superbad64/OpenFighter/Personal Builds/Final Boss Neo/STL/Long sides/side_none.stl

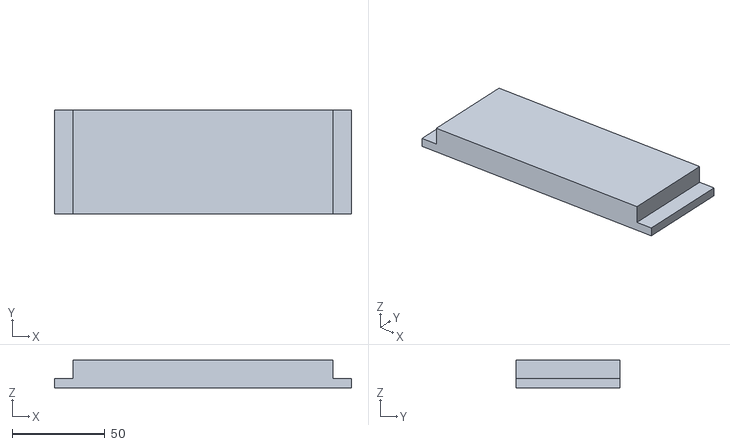
[picture p22: CAD file, 2025-08-16]
Personal Builds/Final Boss Neo/STL/Long sides/side_none.stl
160.0 x 56.0 x 15.0
