superbad64/OpenFighter/Personal Builds/Miniboss Neo/Cut files/miniboss_neo.dxf

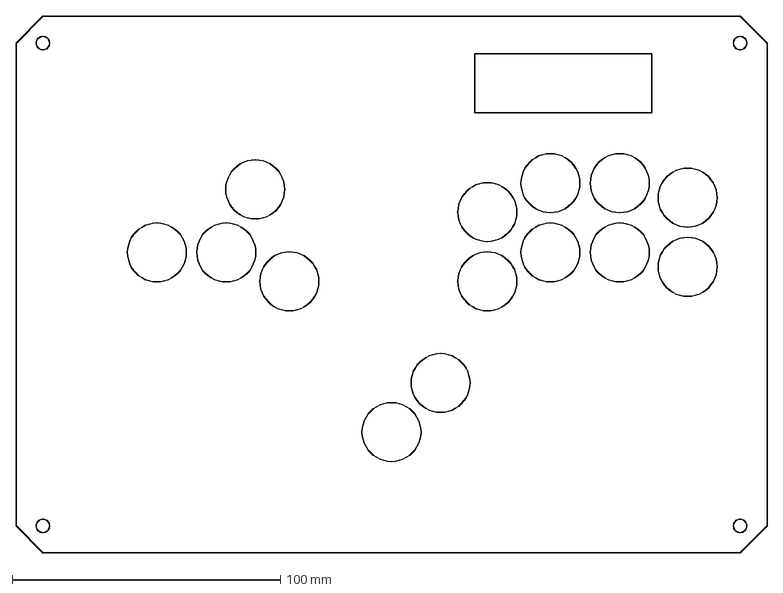
[picture p24: CAD file, 2025-08-24]
Personal Builds/Miniboss Neo/Cut files/miniboss_neo.dxf
280.0 x 200.0 mm
