superbad64/OpenFighter/Personal Builds/Raijin/Production Files/corner.stl

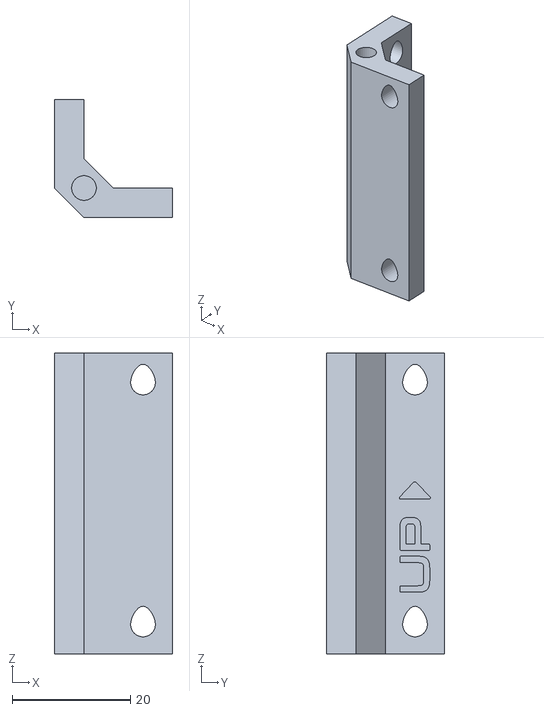
[picture p25: CAD file, 2025-08-24]
Personal Builds/Raijin/Production Files/corner.stl
20.0 x 20.0 x 51.0
