superbad64/OpenFighter/Personal Builds/Raijin/Production Files/Cuts/raijin.spacer.dxf

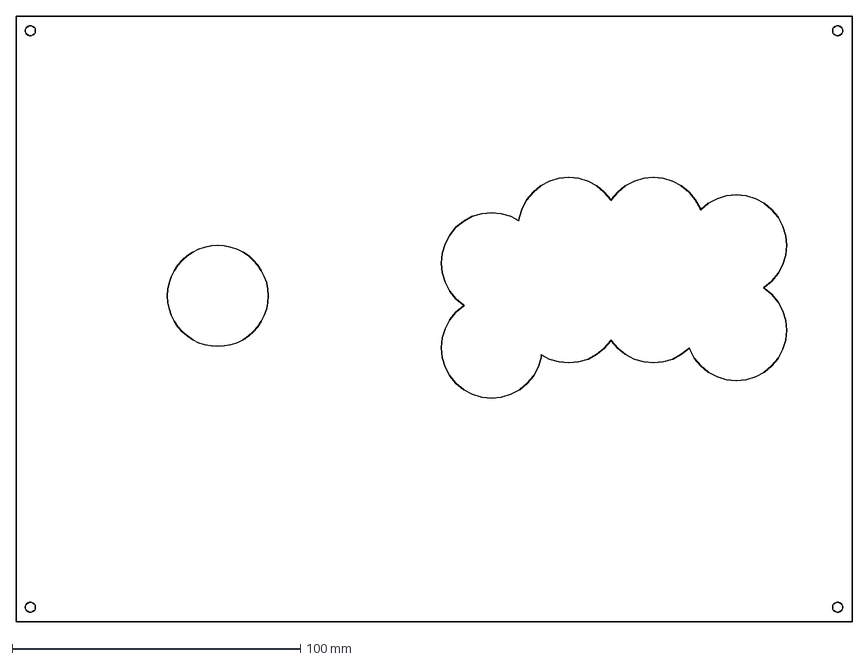
[picture p26: CAD file, 2026-04-07]
Personal Builds/Raijin/Production Files/Cuts/raijin.spacer.dxf
290.0 x 210.0 mm
