superbad64/OpenFighter/Tteokbokki/STL/Bottom Panels/Magnetic/magnetic_bottom_right.stl

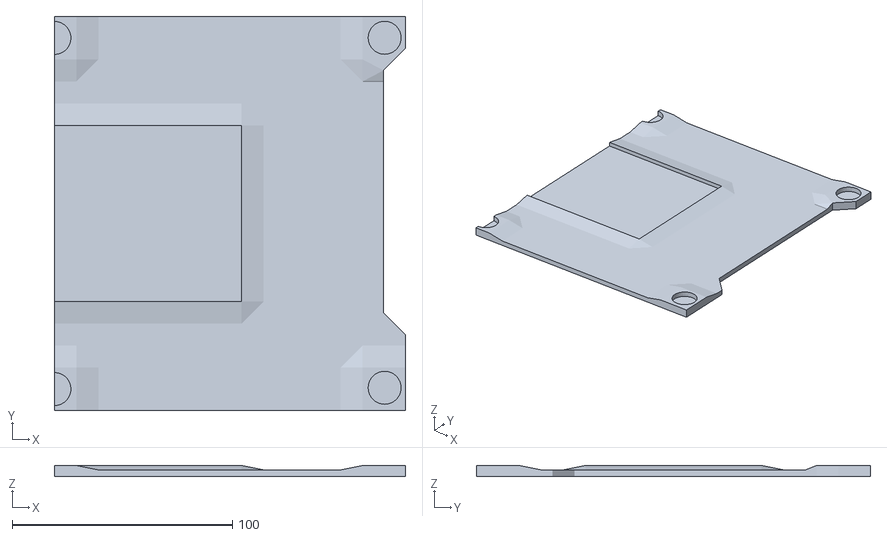
[picture p27: CAD file, 2025-12-30]
Tteokbokki/STL/Bottom Panels/Magnetic/magnetic_bottom_right.stl
159.5 x 179.0 x 5.00
