superbad64/OpenFighter/Tteokbokki/STL/Top Panels/Hitbox/hb_right.stl

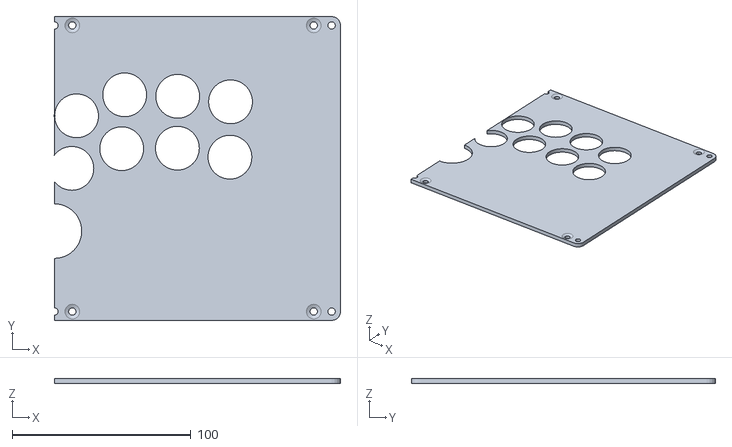
[picture p28: CAD file, 2025-12-30]
Tteokbokki/STL/Top Panels/Hitbox/hb_right.stl
160.0 x 170.0 x 3.00
