superbad64/OpenFighter/Tteokbokki/STL/Top Panels/Sega 2P/30mm/s2p_30mm_left.stl

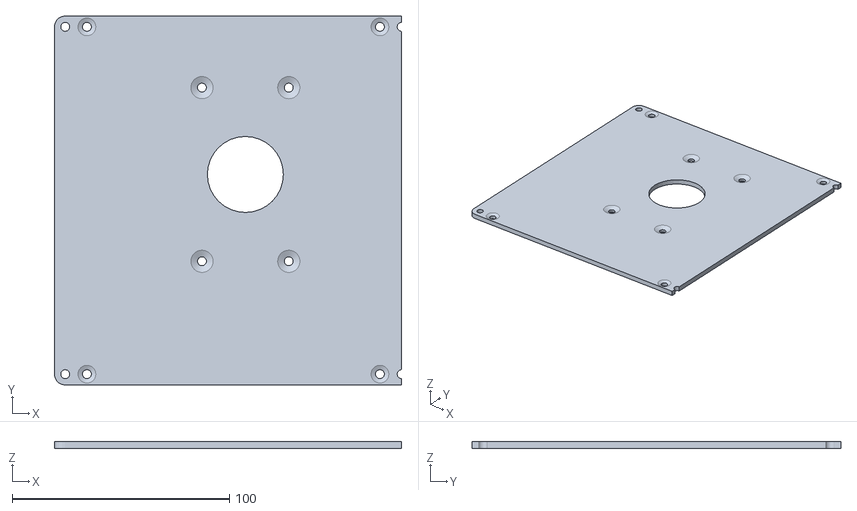
[picture p29: CAD file, 2025-12-30]
Tteokbokki/STL/Top Panels/Sega 2P/30mm/s2p_30mm_left.stl
160.0 x 170.0 x 3.00
