superbad64/OpenFighter/Tteokbokki/STL/Top Panels/WASD/wasd_right.stl

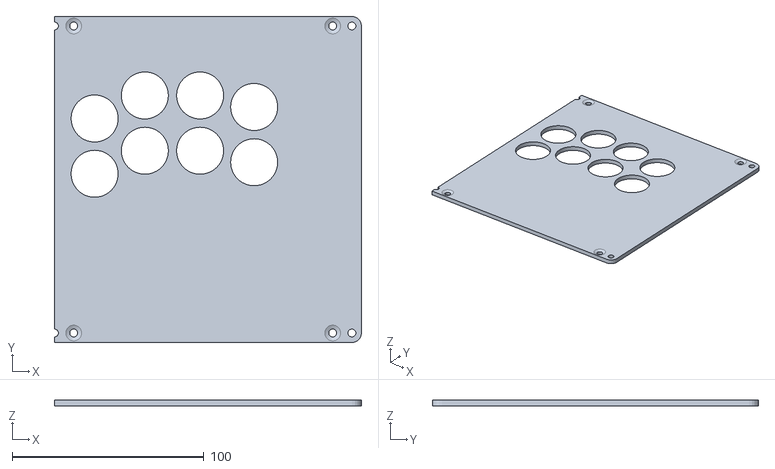
[picture p30: CAD file, 2025-12-30]
Tteokbokki/STL/Top Panels/WASD/wasd_right.stl
160.0 x 170.0 x 3.00
