superbad64/OpenFighter/Unhinged/Cut files/WASD.dxf

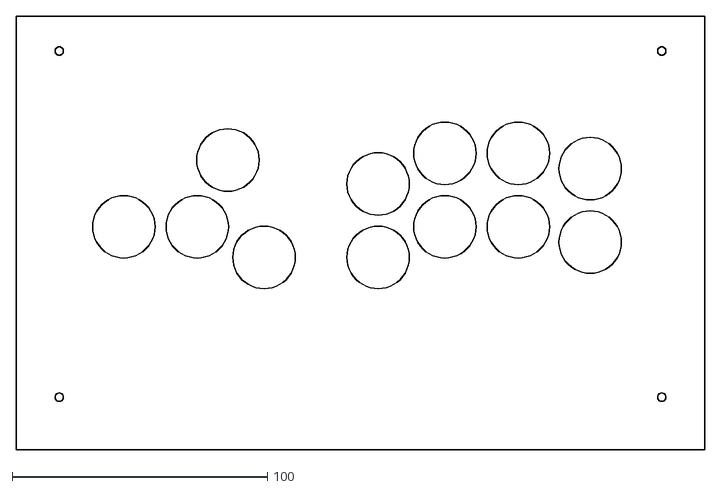
[picture p31: CAD file, 2025-08-24]
Unhinged/Cut files/WASD.dxf
270.0 x 169.9
