superbad64/OpenFighter/Unhinged/STL/Hinges/long arm.stl

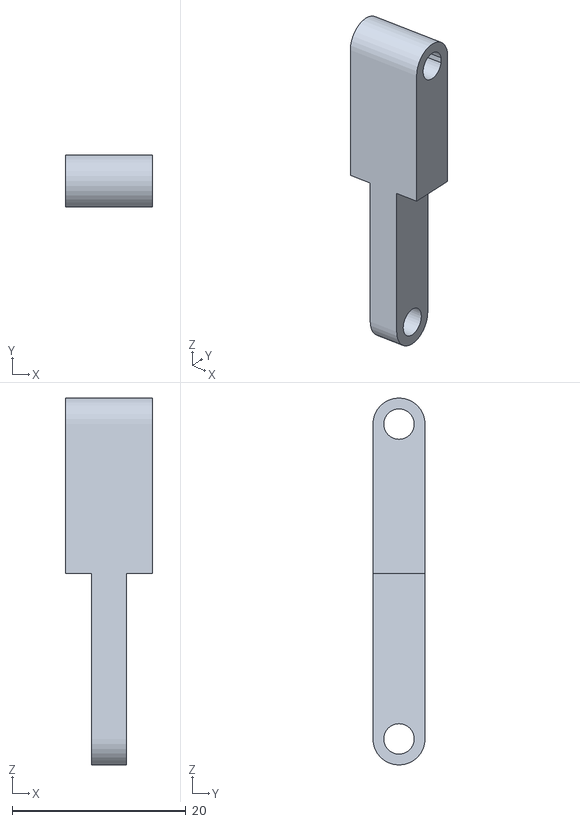
[picture p32: CAD file, 2025-02-27]
Unhinged/STL/Hinges/long arm.stl
10.0 x 6.00 x 42.2
