superbad64/OpenFighter/Unhinged/STL/left.stl

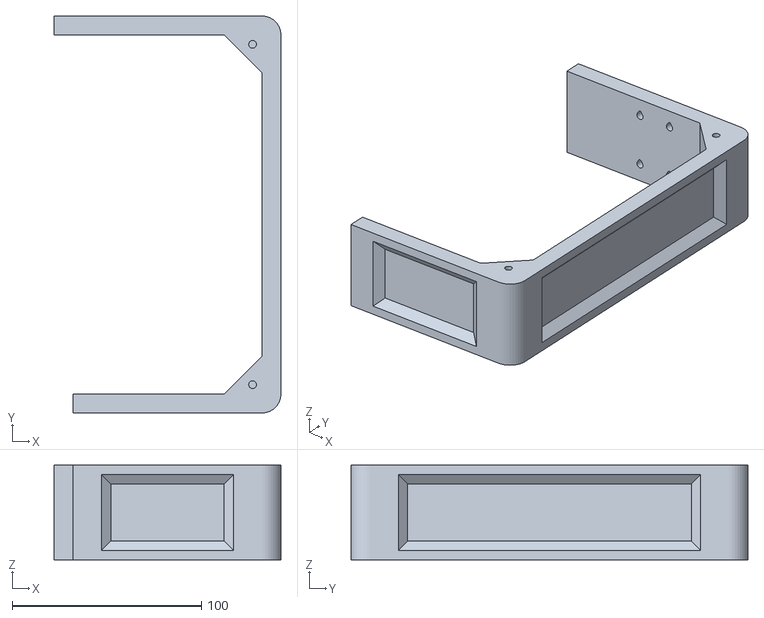
[picture p33: CAD file, 2025-02-27]
Unhinged/STL/left.stl
120.0 x 210.0 x 50.0
