superbad64/OpenFighter/Unhinged/STL/Top/pin.stl

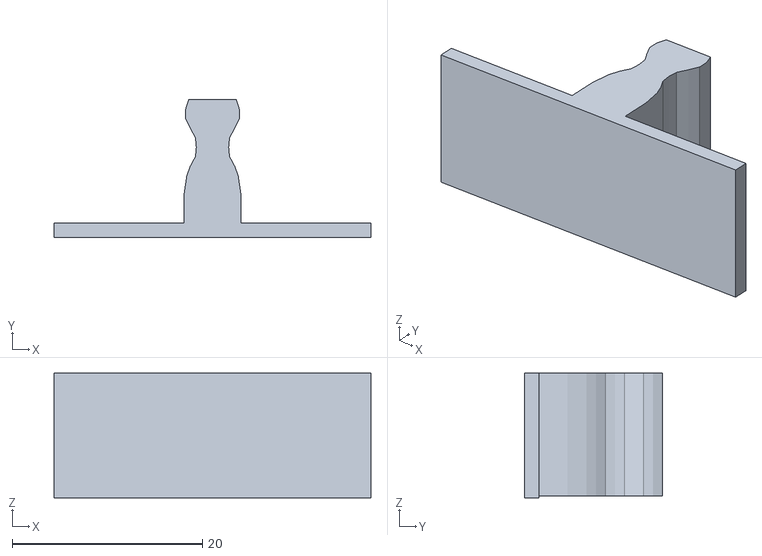
[picture p34: CAD file, 2025-02-27]
Unhinged/STL/Top/pin.stl
33.4 x 14.5 x 13.1
