superbad64/OpenFighter/Wanderer/Production Files/STL/right.stl

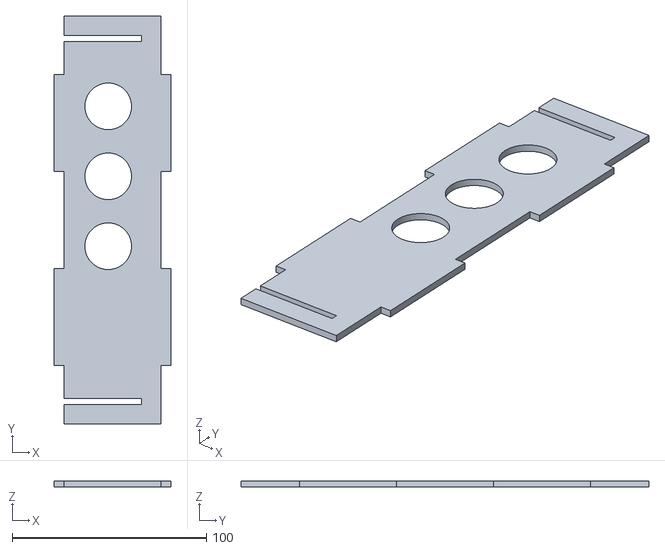
[picture p35: CAD file, 2025-12-16]
Wanderer/Production Files/STL/right.stl
60.0 x 210.0 x 3.00
