superbad64/OpenFighter/Ogre/Production Files/Laser Cut Templates/wing external.dxf

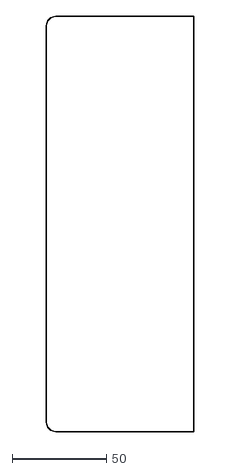
[picture p37: CAD file, 2025-08-24]
Ogre/Production Files/Laser Cut Templates/wing external.dxf
78.0 x 220.0
