superbad64/OpenFighter/Ogre/Production Files/STL/Common/bottom.stl

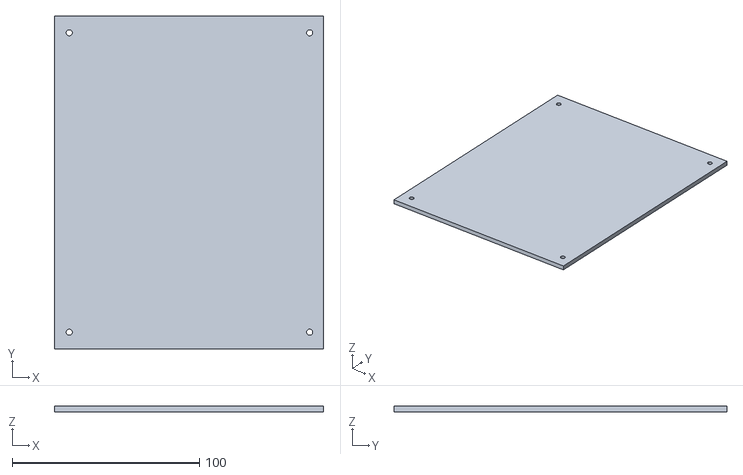
[picture p38: CAD file, 2025-02-27]
Ogre/Production Files/STL/Common/bottom.stl
144.0 x 178.0 x 3.00
