superbad64/OpenFighter/Ork/Production Files/shortside.stl

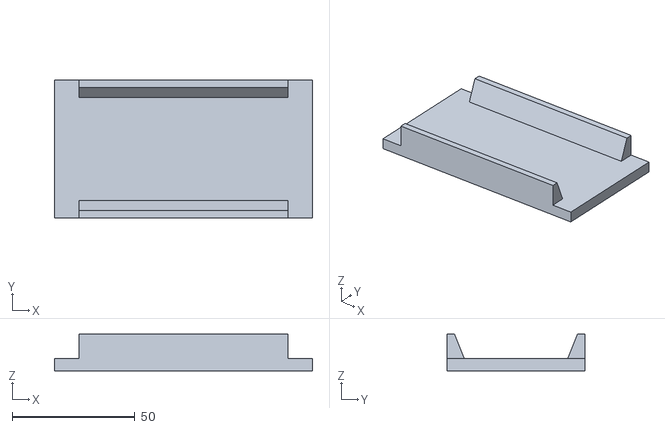
[picture p40: CAD file, 2025-08-16]
Ork/Production Files/shortside.stl
105.0 x 56.0 x 15.0
