superbad64/OpenFighter/Ork/Production Files/WASD/wasd_topright.stl

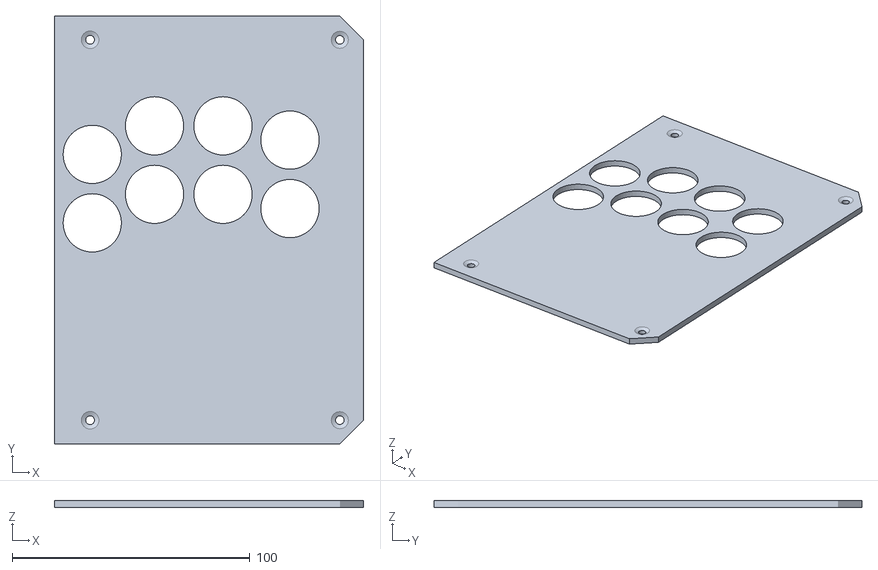
[picture p41: CAD file, 2025-08-16]
Ork/Production Files/WASD/wasd_topright.stl
130.0 x 180.0 x 3.00
