superbad64/OpenFighter/Personal Builds/Final Boss Neo/Laser Cuts/fbneo.topright.dxf

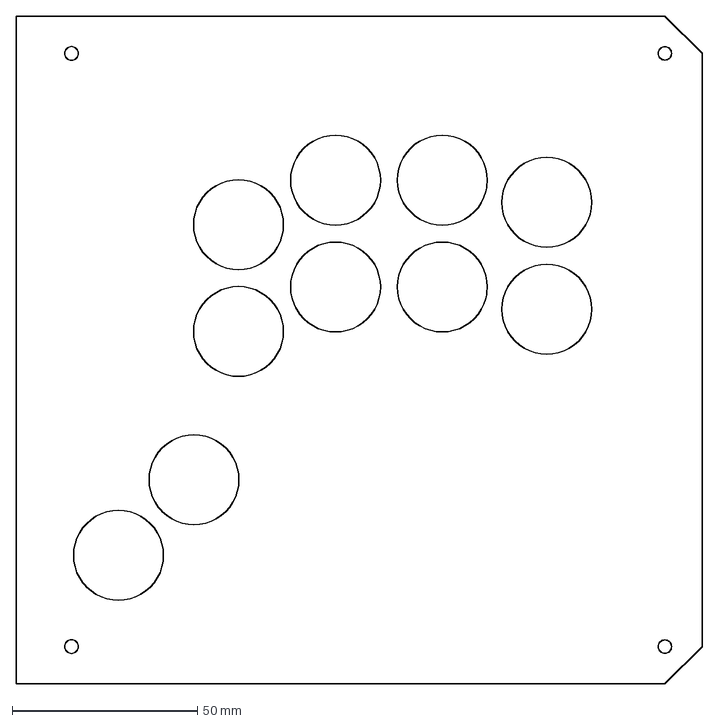
[picture p42: CAD file, 2025-08-24]
Personal Builds/Final Boss Neo/Laser Cuts/fbneo.topright.dxf
185.0 x 180.0 mm
