superbad64/OpenFighter/Personal Builds/Final Boss Neo/STL/Long sides/side_vent.stl

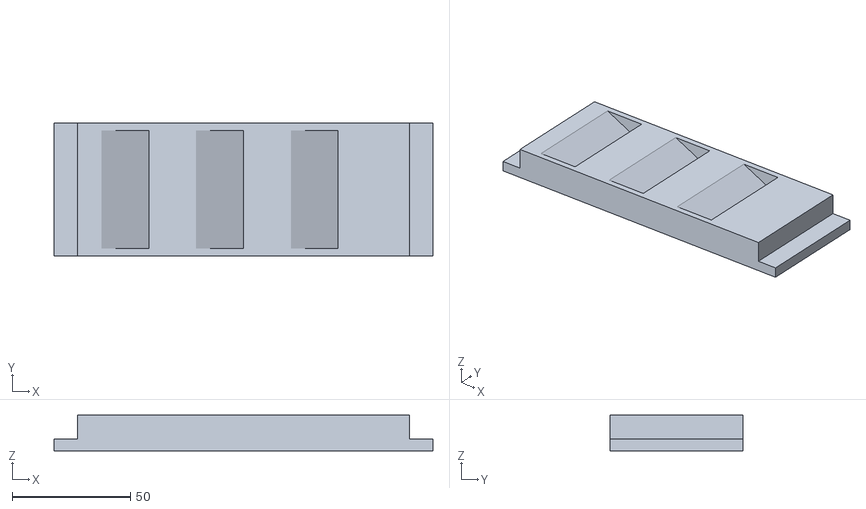
[picture p43: CAD file, 2025-08-16]
Personal Builds/Final Boss Neo/STL/Long sides/side_vent.stl
160.0 x 56.0 x 15.0
