superbad64/OpenFighter/Personal Builds/Final Boss Neo/STL/Surround Plates/surround_nunchuk_backplate.stl

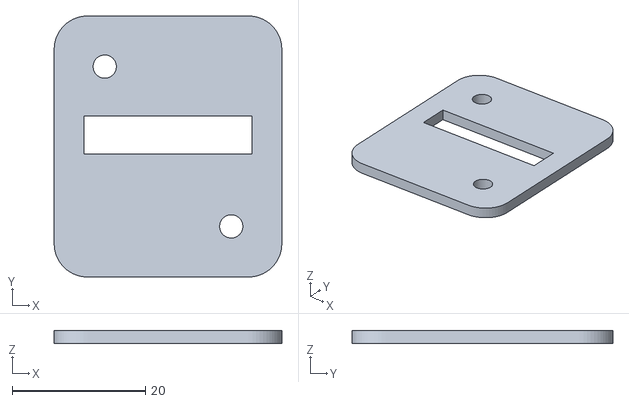
[picture p44: CAD file, 2025-08-16]
Personal Builds/Final Boss Neo/STL/Surround Plates/surround_nunchuk_backplate.stl
34.2 x 39.2 x 2.00
