superbad64/OpenFighter/Personal Builds/Final Boss Neo/STL/top_right.stl

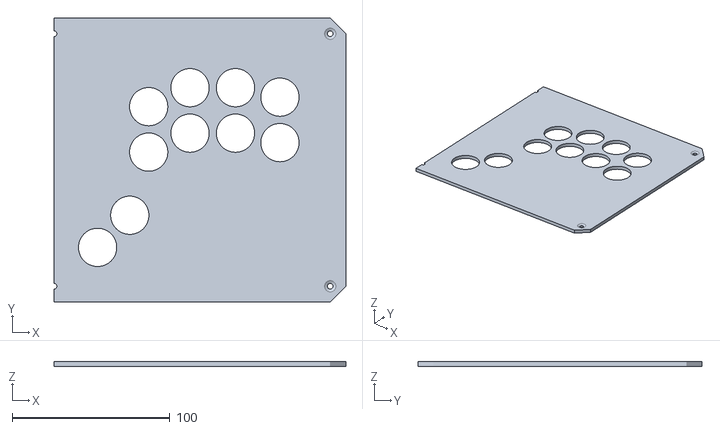
[picture p45: CAD file, 2025-08-16]
Personal Builds/Final Boss Neo/STL/top_right.stl
185.0 x 180.0 x 3.00
