superbad64/OpenFighter/Personal Builds/Raijin/Production Files/bracket.stl

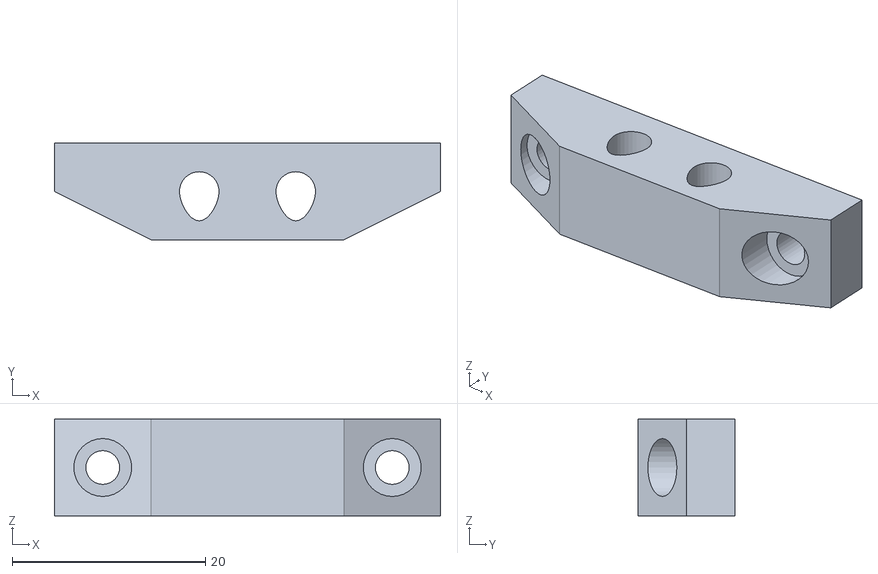
[picture p46: CAD file, 2025-08-24]
Personal Builds/Raijin/Production Files/bracket.stl
40.0 x 10.0 x 10.0
