superbad64/OpenFighter/Personal Builds/Raijin/Production Files/Cuts/raijin.dxf

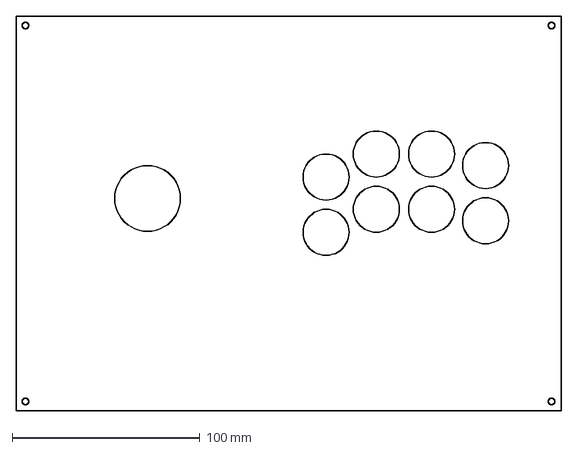
[picture p47: CAD file, 2025-08-24]
Personal Builds/Raijin/Production Files/Cuts/raijin.dxf
290.0 x 210.0 mm
