superbad64/OpenFighter/Tteokbokki/STL/Top Panels/Hitbox/hb_left.stl

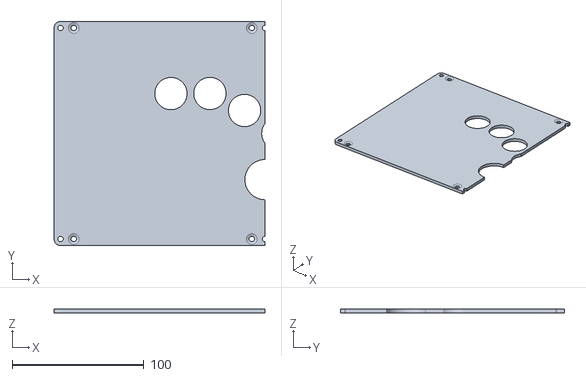
[picture p48: CAD file, 2025-12-30]
Tteokbokki/STL/Top Panels/Hitbox/hb_left.stl
160.0 x 170.0 x 3.00
