superbad64/OpenFighter/Unhinged/Cut files/Sega 2P.dxf

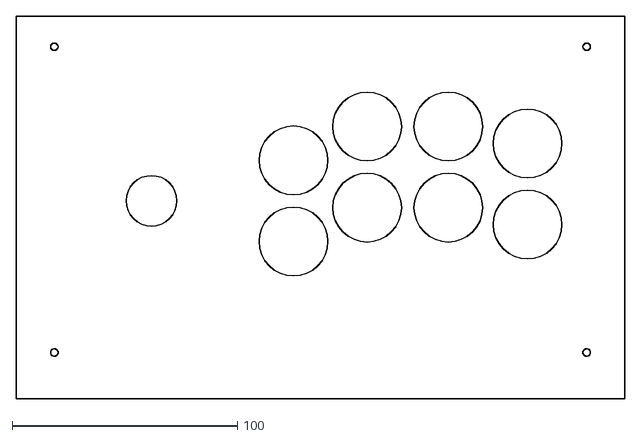
[picture p50: CAD file, 2025-08-24]
Unhinged/Cut files/Sega 2P.dxf
270.0 x 169.9
