superbad64/OpenFighter/Unhinged/STL/bottomright.stl

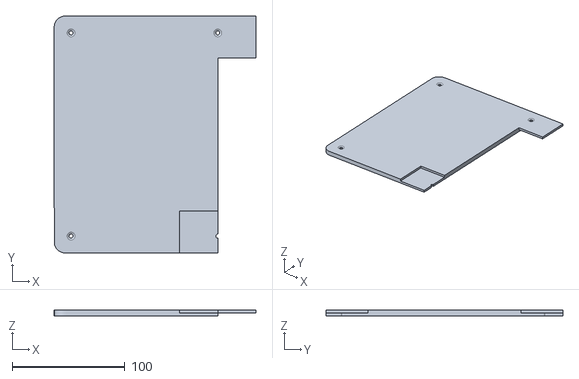
[picture p51: CAD file, 2025-02-27]
Unhinged/STL/bottomright.stl
178.8 x 210.0 x 5.00
