superbad64/OpenFighter/Unhinged/STL/Hinges/hinge base.stl

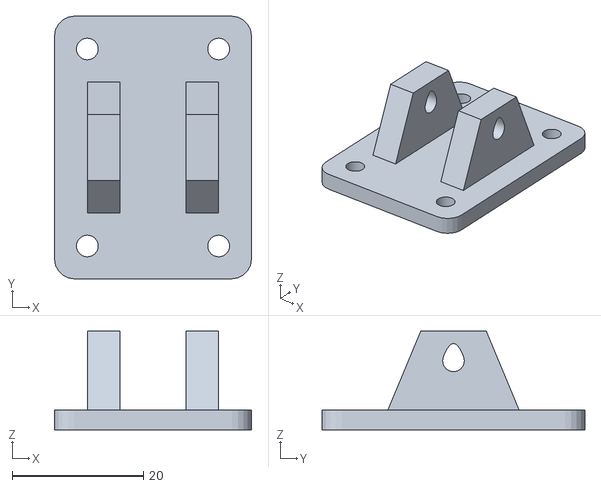
[picture p52: CAD file, 2025-02-27]
Unhinged/STL/Hinges/hinge base.stl
30.0 x 40.0 x 15.0
