superbad64/OpenFighter/Unhinged/STL/Top/bezel_right.stl

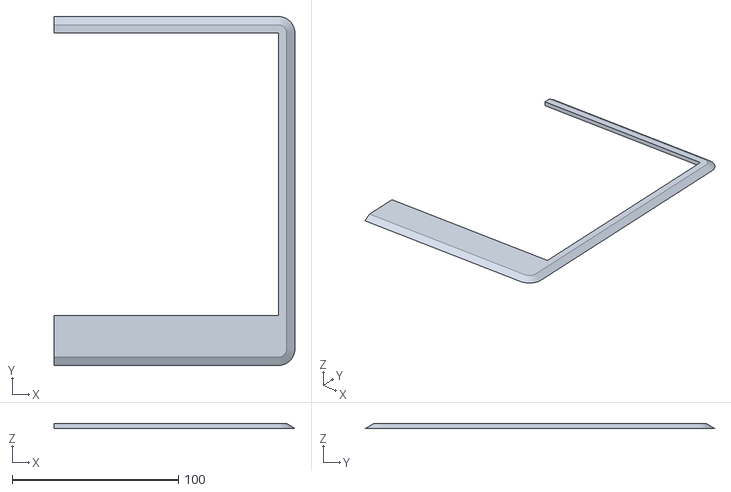
[picture p53: CAD file, 2025-02-27]
Unhinged/STL/Top/bezel_right.stl
145.0 x 210.0 x 3.00
