superbad64/OpenFighter/Wanderer/Production Files/STL/Top Panel/HitBox/right.stl

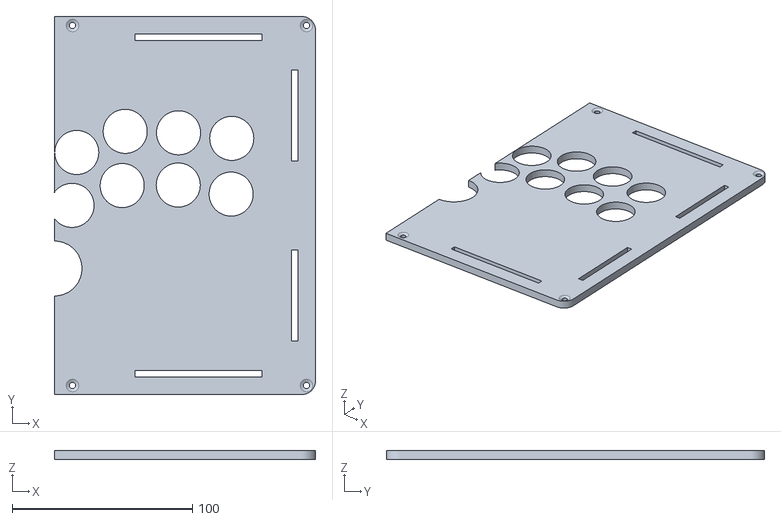
[picture p55: CAD file, 2025-12-16]
Wanderer/Production Files/STL/Top Panel/HitBox/right.stl
145.0 x 210.0 x 5.00
