superbad64/OpenFighter/Ogre/Production Files/Laser Cut Templates/front.dxf

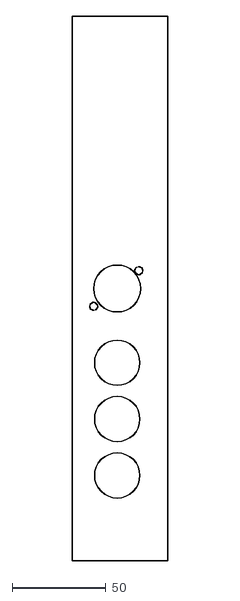
[picture p58: CAD file, 2025-08-24]
Ogre/Production Files/Laser Cut Templates/front.dxf
51.0 x 290.0
