superbad64/OpenFighter/Ork/Production Files/right.stl

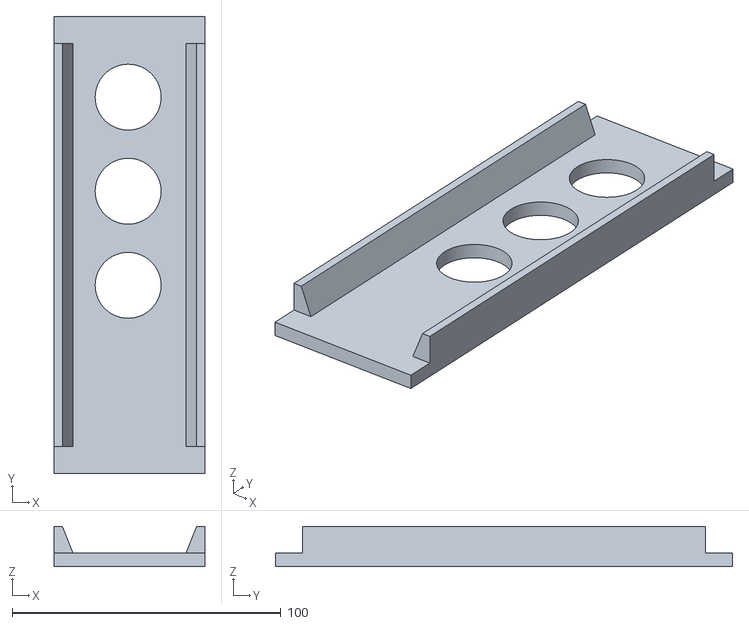
[picture p59: CAD file, 2025-08-16]
Ork/Production Files/right.stl
56.0 x 170.0 x 15.0
