superbad64/OpenFighter/Personal Builds/Final Boss Neo/Laser Cuts/fbneo.dxf

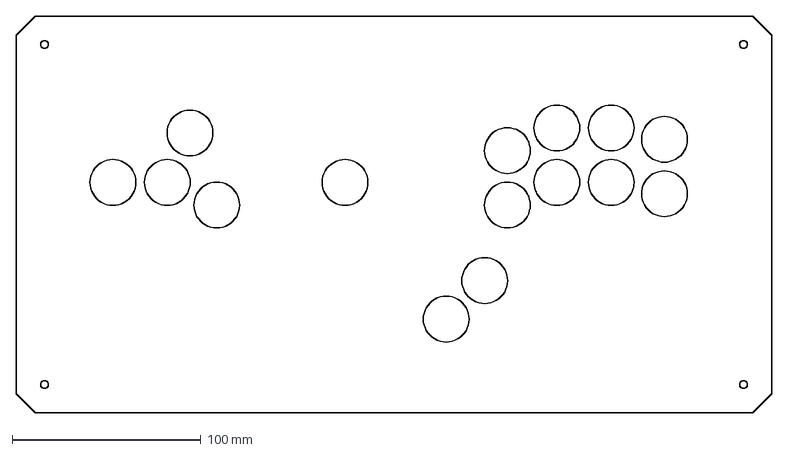
[picture p60: CAD file, 2025-08-24]
Personal Builds/Final Boss Neo/Laser Cuts/fbneo.dxf
400.0 x 210.0 mm
