superbad64/OpenFighter/Personal Builds/Raijin/Production Files/southeast.stl

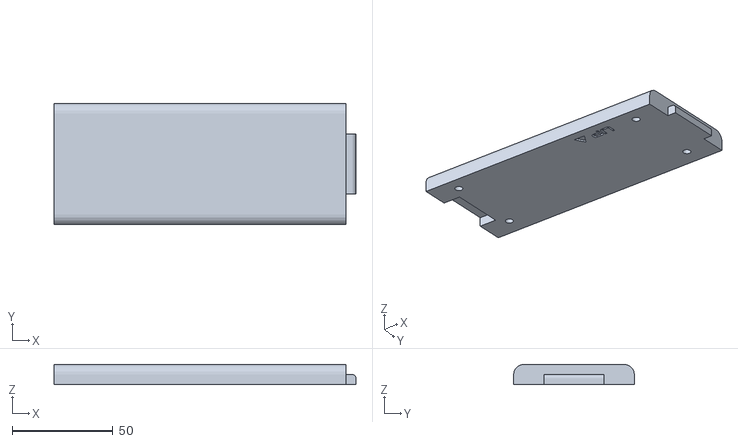
[picture p62: CAD file, 2025-08-24]
Personal Builds/Raijin/Production Files/southeast.stl
150.0 x 60.0 x 10.0
