superbad64/OpenFighter/Tteokbokki/STL/Bottom Panels/Magnetic/magnetic_bottom_center.stl

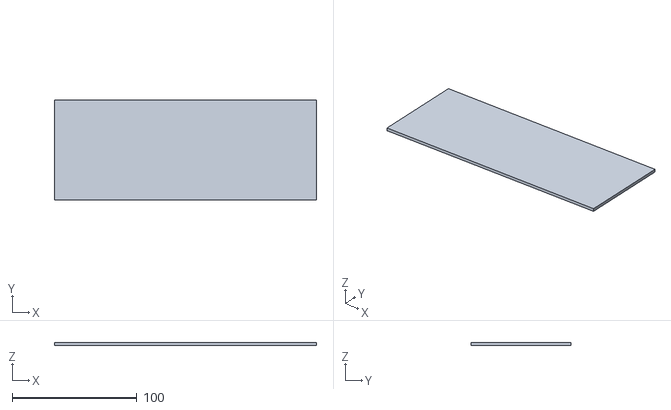
[picture p63: CAD file, 2025-12-30]
Tteokbokki/STL/Bottom Panels/Magnetic/magnetic_bottom_center.stl
210.0 x 80.0 x 2.50
