superbad64/OpenFighter/Unhinged/Cut files/HitBox.dxf

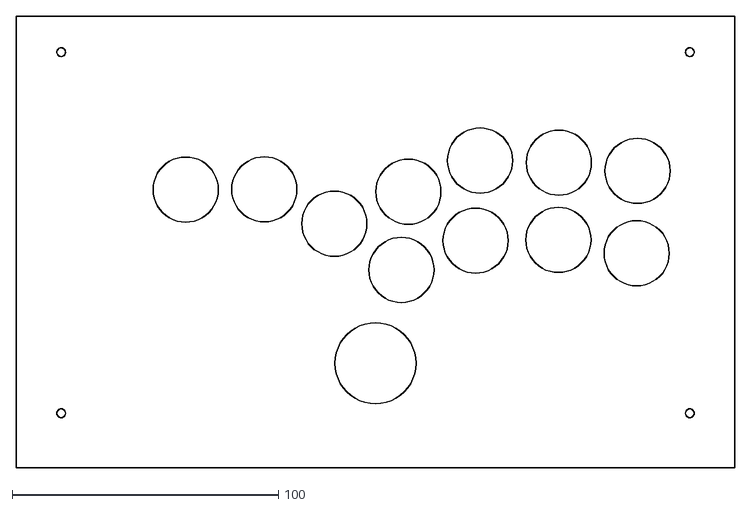
[picture p64: CAD file, 2025-08-24]
Unhinged/Cut files/HitBox.dxf
270.0 x 169.9
