superbad64/OpenFighter/Unhinged/STL/Hinges/short arm.stl

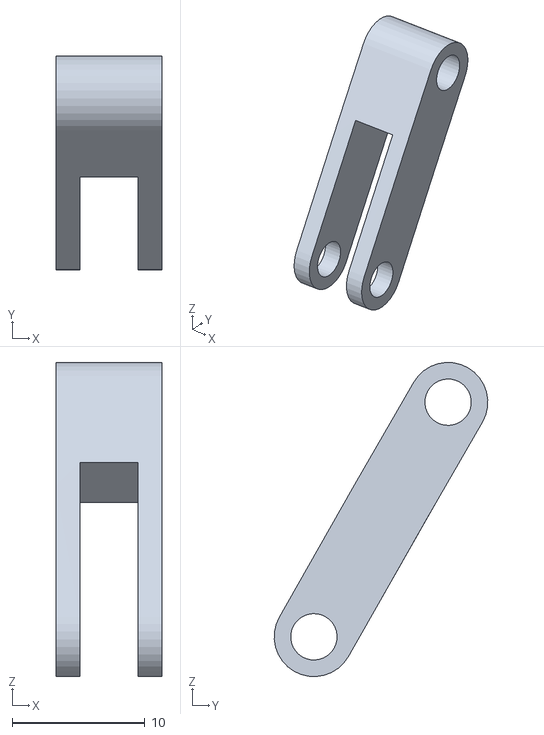
[picture p65: CAD file, 2025-02-27]
Unhinged/STL/Hinges/short arm.stl
8.00 x 16.1 x 23.7
