superbad64/OpenFighter/Wanderer/Production Files/STL/centerfront.stl

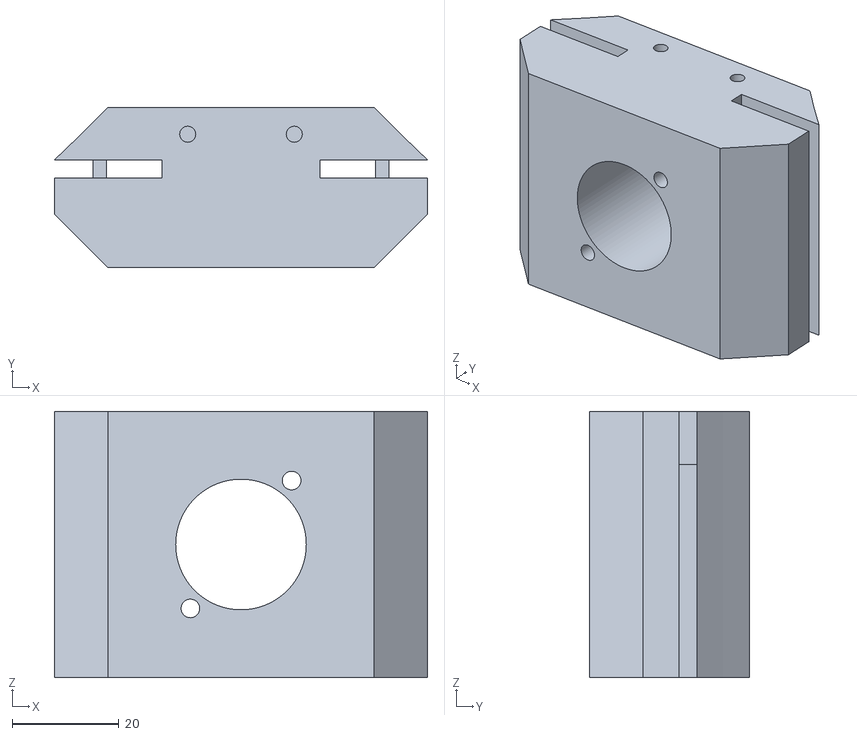
[picture p67: CAD file, 2025-12-16]
Wanderer/Production Files/STL/centerfront.stl
70.0 x 30.0 x 50.0
