superbad64/OpenFighter/Wanderer/Production Files/STL/Top Panel/Sega 2P/left JP.stl

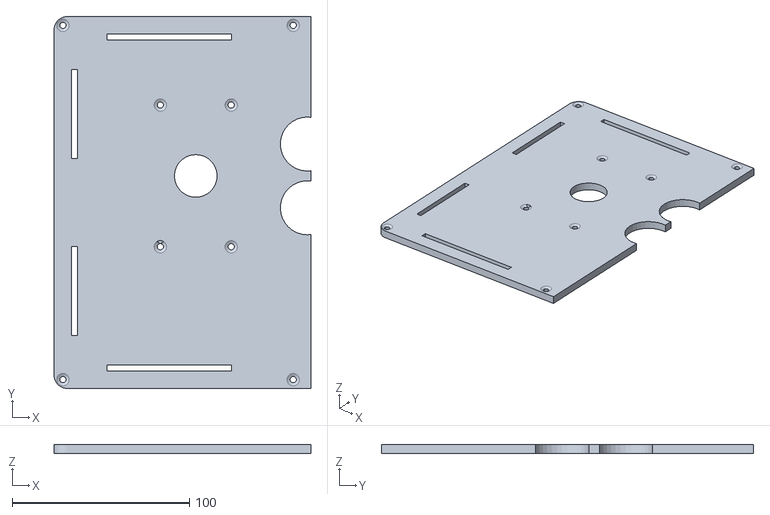
[picture p68: CAD file, 2025-12-16]
Wanderer/Production Files/STL/Top Panel/Sega 2P/left JP.stl
145.0 x 210.0 x 5.00
