superbad64/OpenFighter/Ogre/Production Files/Laser Cut Templates/cuts 2.dxf

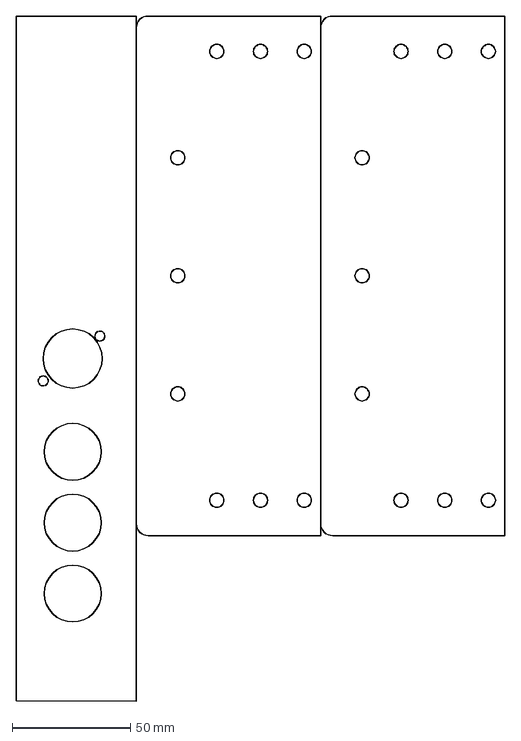
[picture p69: CAD file, 2025-08-24]
Ogre/Production Files/Laser Cut Templates/cuts 2.dxf
207.0 x 290.0 mm
