superbad64/OpenFighter/Ogre/Production Files/STL/Wood panels/back panel.stl

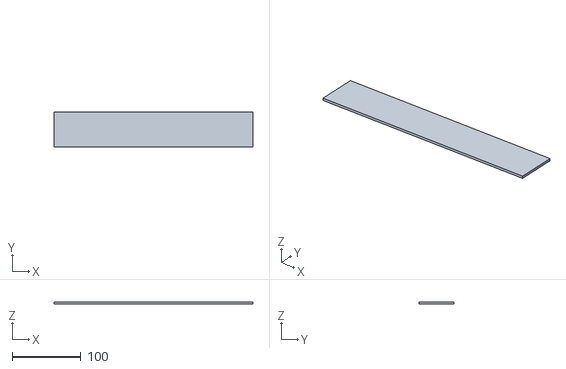
[picture p70: CAD file, 2025-02-27]
Ogre/Production Files/STL/Wood panels/back panel.stl
290.0 x 51.0 x 3.00
