superbad64/OpenFighter/Ork/Production Files/front.stl

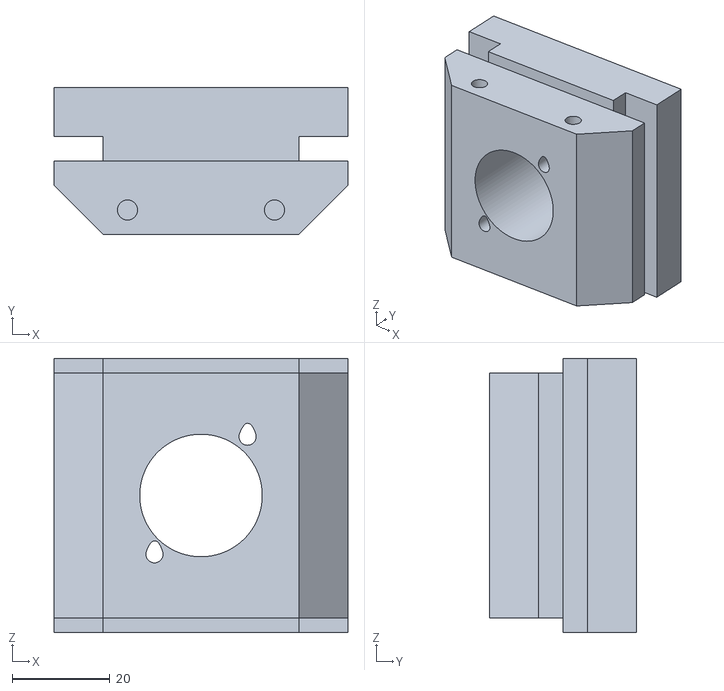
[picture p71: CAD file, 2025-08-16]
Ork/Production Files/front.stl
60.0 x 30.0 x 56.0
