superbad64/OpenFighter/Personal Builds/Raijin/Production Files/topright-withspacer.stl

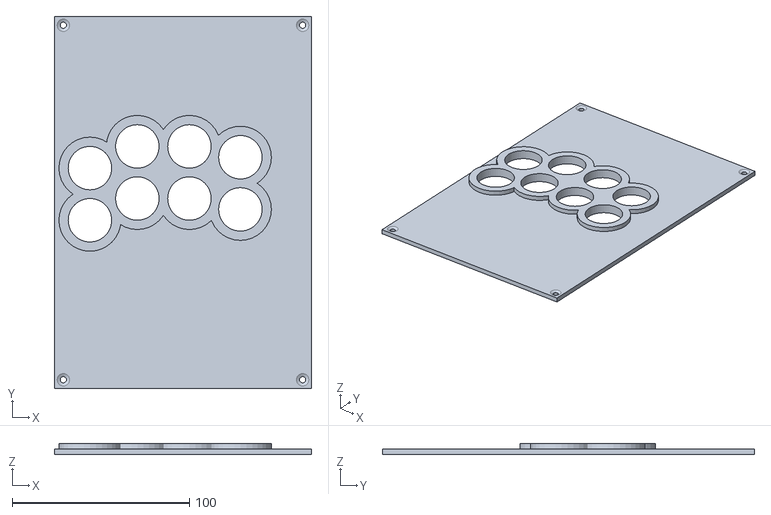
[picture p73: CAD file, 2025-08-24]
Personal Builds/Raijin/Production Files/topright-withspacer.stl
145.0 x 210.0 x 6.00
