superbad64/OpenFighter/Unhinged/STL/dowel.stl

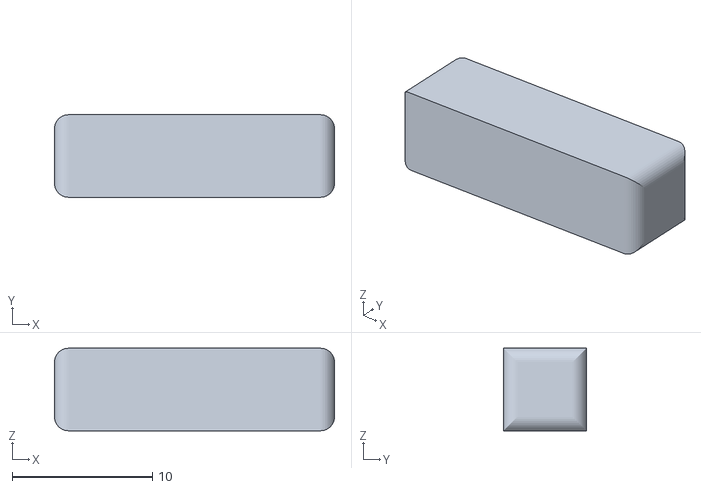
[picture p74: CAD file, 2025-02-27]
Unhinged/STL/dowel.stl
20.0 x 5.90 x 5.90
