superbad64/OpenFighter/Ogre/Production Files/Laser Cut Templates/#back.dxf

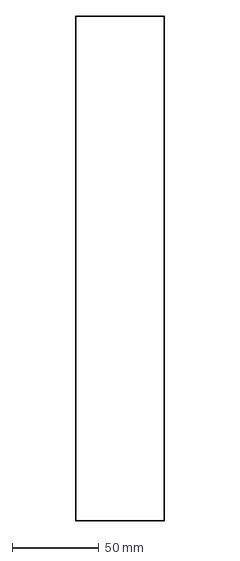
[picture p76: CAD file, 2025-08-24]
Ogre/Production Files/Laser Cut Templates/#back.dxf
51.0 x 290.0 mm
