superbad64/OpenFighter/Ogre/Production Files/STL/Common/fender right.stl

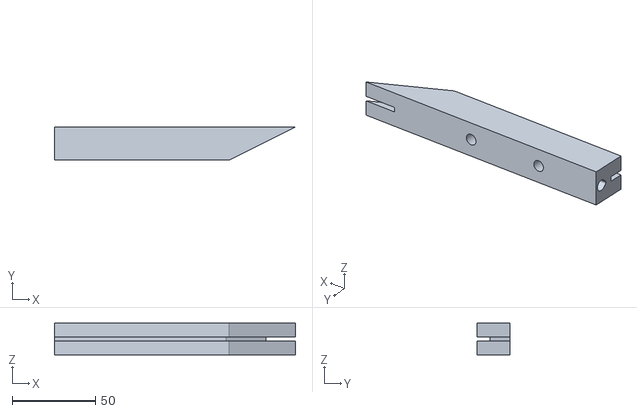
[picture p77: CAD file, 2025-02-27]
Ogre/Production Files/STL/Common/fender right.stl
145.0 x 20.0 x 19.0
