superbad64/OpenFighter/Ogre/Production Files/STL/Wood panels/wing inner.stl

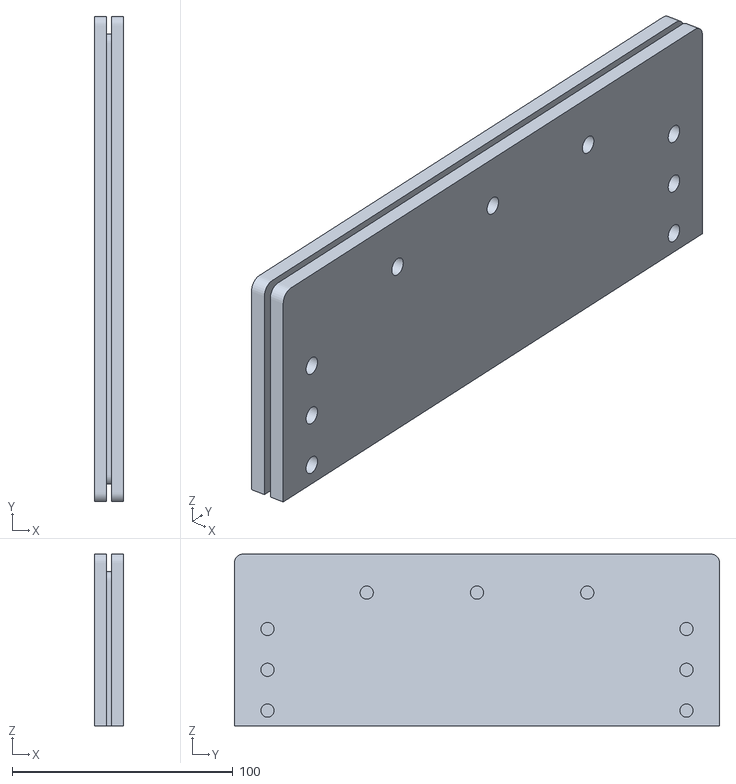
[picture p78: CAD file, 2025-02-27]
Ogre/Production Files/STL/Wood panels/wing inner.stl
13.0 x 220.0 x 78.0
