superbad64/OpenFighter/Ork/Production Files/back.stl

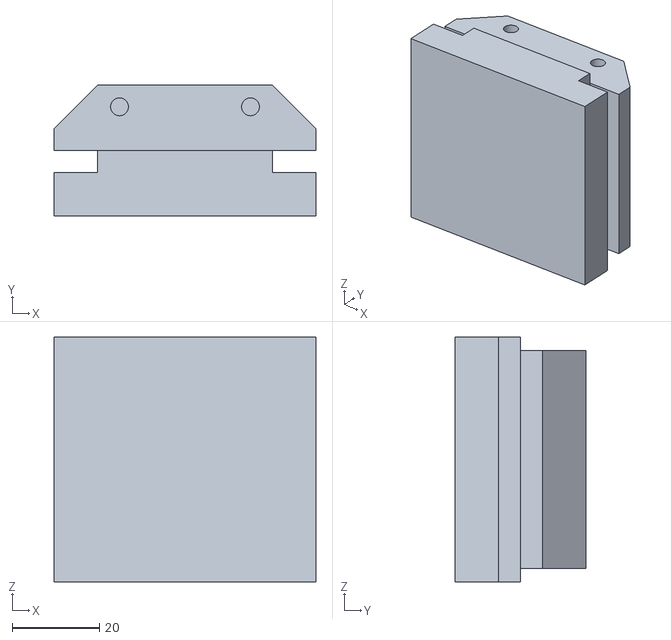
[picture p79: CAD file, 2025-08-16]
Ork/Production Files/back.stl
60.0 x 30.0 x 56.0
