superbad64/OpenFighter/Personal Builds/Final Boss Neo/STL/Surround Plates/surround_switch.stl

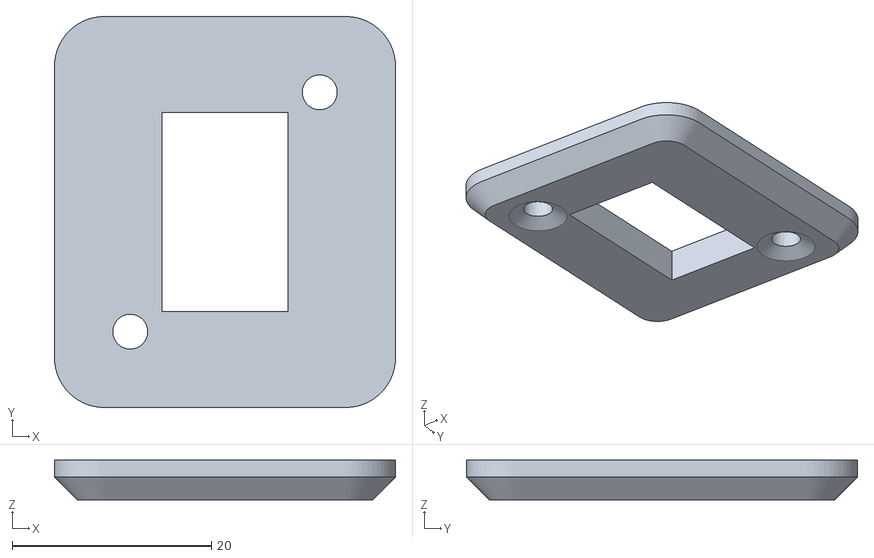
[picture p80: CAD file, 2025-08-16]
Personal Builds/Final Boss Neo/STL/Surround Plates/surround_switch.stl
34.2 x 39.2 x 4.00
