superbad64/OpenFighter/Personal Builds/Raijin/Production Files/southwest.stl

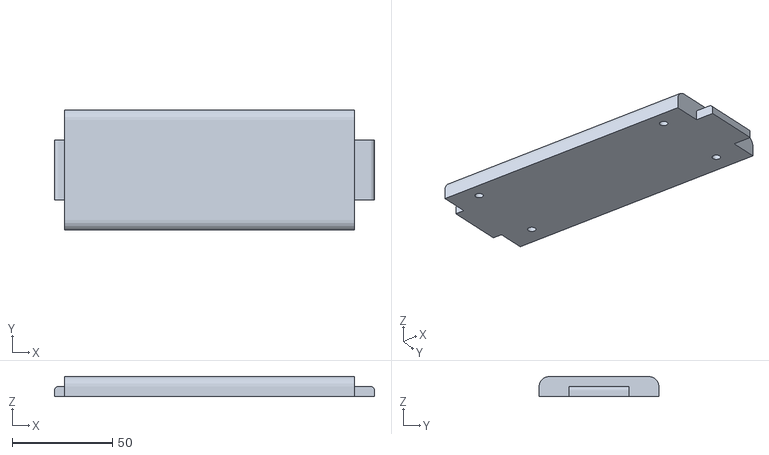
[picture p81: CAD file, 2025-08-24]
Personal Builds/Raijin/Production Files/southwest.stl
160.0 x 60.0 x 10.0
