superbad64/OpenFighter/Unhinged/STL/centerfront.stl

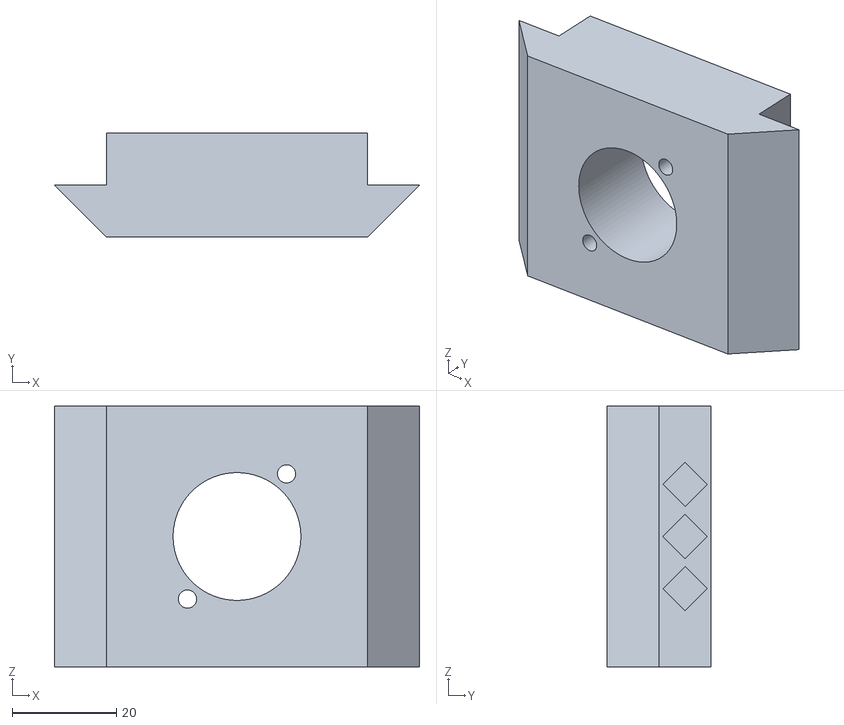
[picture p82: CAD file, 2025-02-27]
Unhinged/STL/centerfront.stl
70.0 x 20.0 x 50.0
