superbad64/OpenFighter/Wanderer/Production Files/STL/bottom.stl

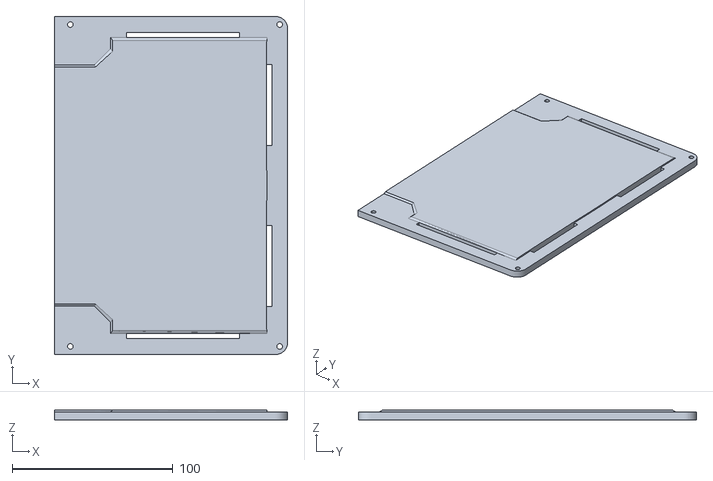
[picture p83: CAD file, 2025-12-16]
Wanderer/Production Files/STL/bottom.stl
145.0 x 210.0 x 6.00
