superbad64/OpenFighter/Ogre/Production Files/Laser Cut Templates/wing internal.dxf

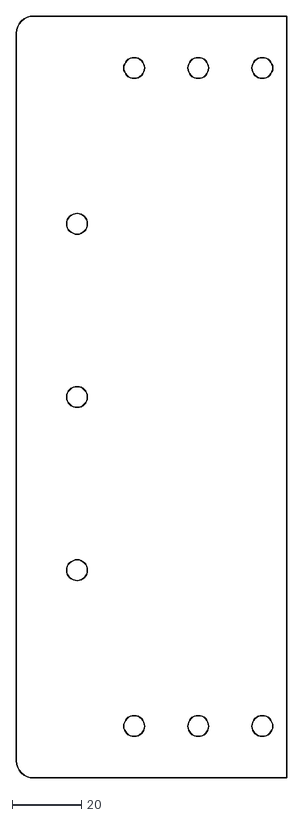
[picture p84: CAD file, 2025-08-24]
Ogre/Production Files/Laser Cut Templates/wing internal.dxf
78.0 x 220.0
