superbad64/OpenFighter/Ork/Production Files/left.stl

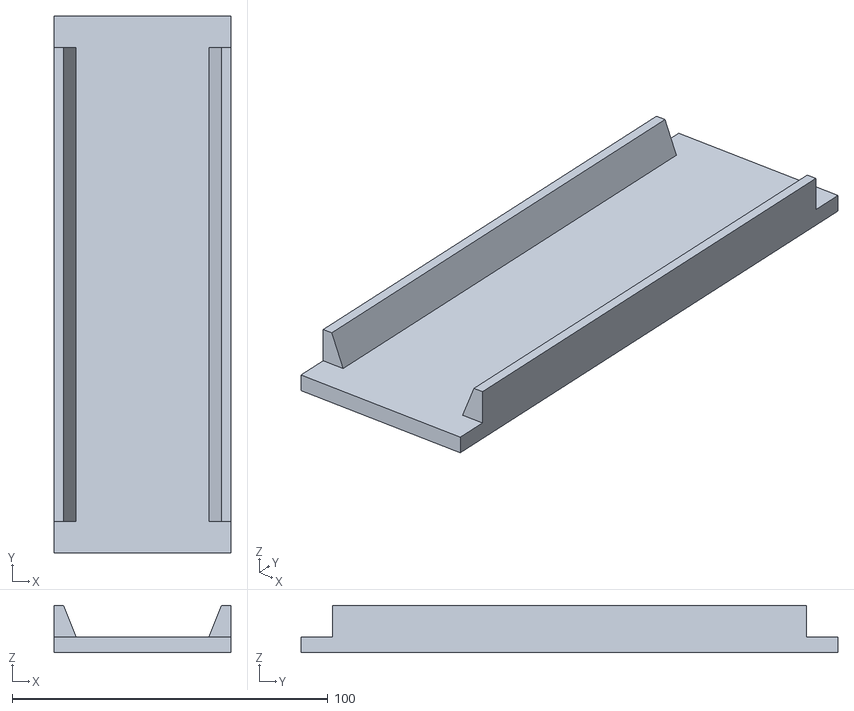
[picture p85: CAD file, 2025-08-16]
Ork/Production Files/left.stl
56.0 x 170.0 x 15.0
