superbad64/OpenFighter/Personal Builds/Miniboss Neo/Print files/text.stl

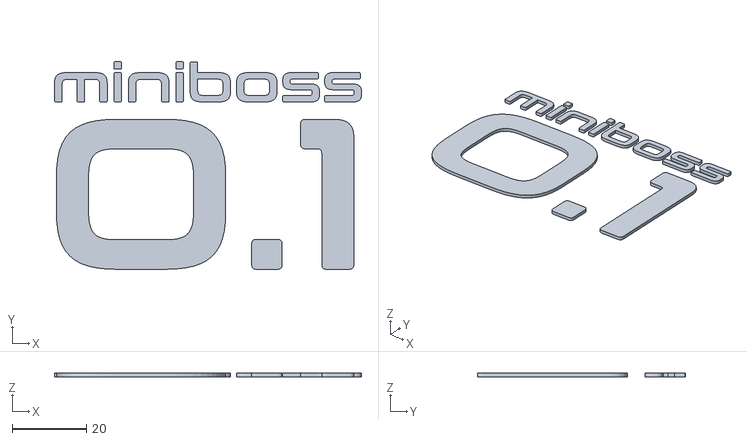
[picture p86: CAD file, 2025-08-16]
Personal Builds/Miniboss Neo/Print files/text.stl
82.6 x 55.8 x 1.00
