superbad64/OpenFighter/Personal Builds/Raijin/Production Files/left.stl

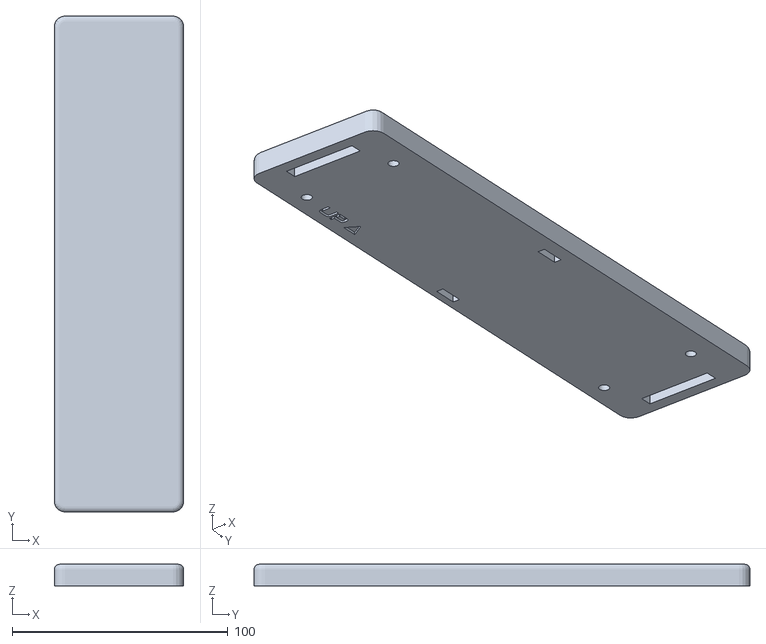
[picture p87: CAD file, 2025-08-24]
Personal Builds/Raijin/Production Files/left.stl
60.0 x 230.0 x 10.0
