superbad64/OpenFighter/Unhinged/STL/centerback.stl

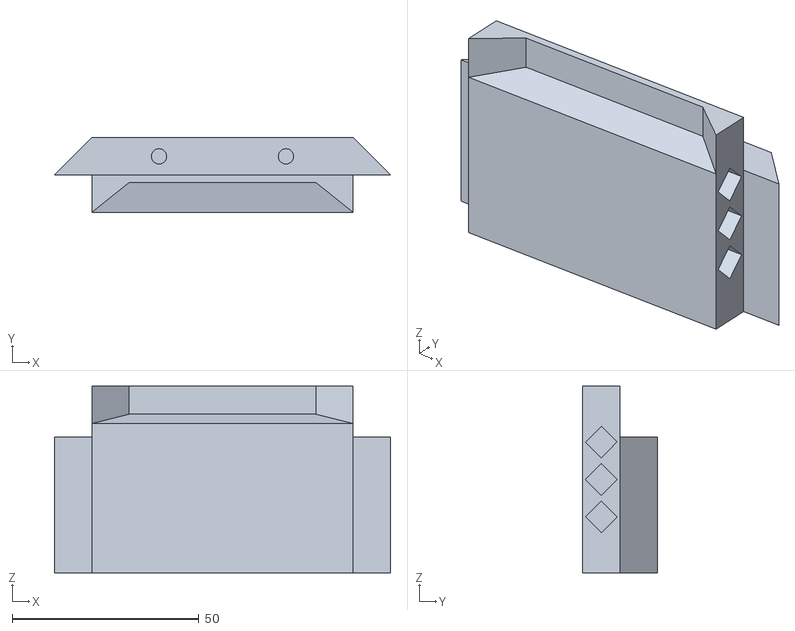
[picture p88: CAD file, 2025-02-27]
Unhinged/STL/centerback.stl
90.0 x 20.0 x 50.0
