superbad64/OpenFighter/Wanderer/Production Files/STL/bridge.stl

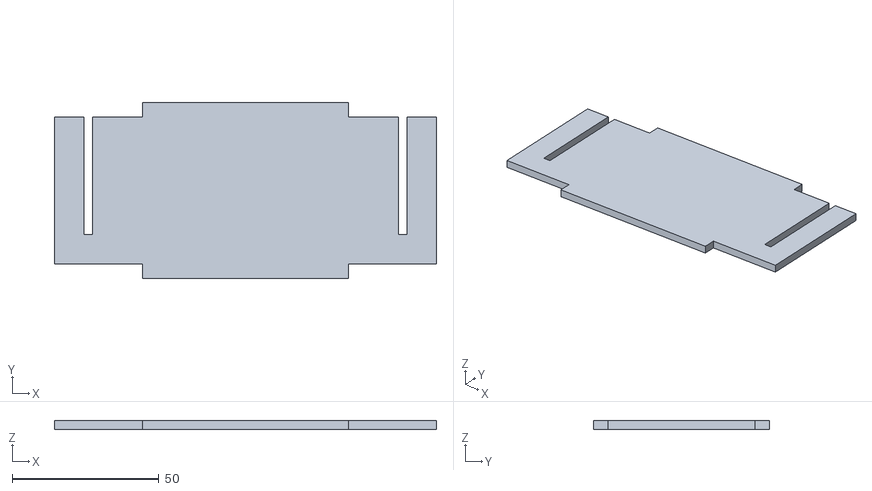
[picture p89: CAD file, 2025-03-14]
Wanderer/Production Files/STL/bridge.stl
130.0 x 60.0 x 3.00
