superbad64/OpenFighter/Ogre/Production Files/Laser Cut Templates/acrylic.dxf

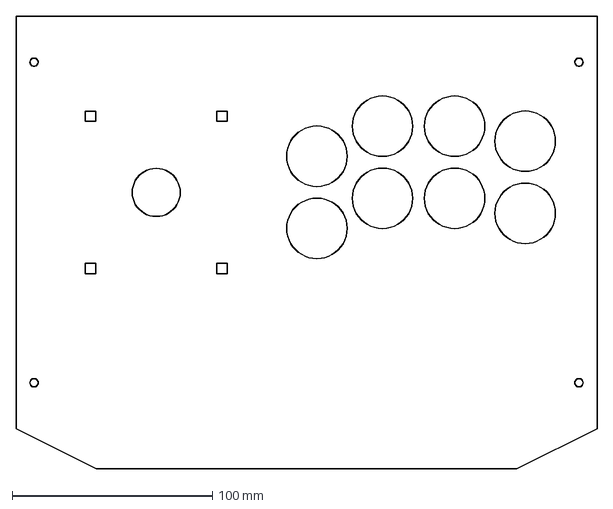
[picture p90: CAD file, 2025-08-24]
Ogre/Production Files/Laser Cut Templates/acrylic.dxf
290.0 x 226.0 mm
