superbad64/OpenFighter/Ork/Production Files/corner.stl

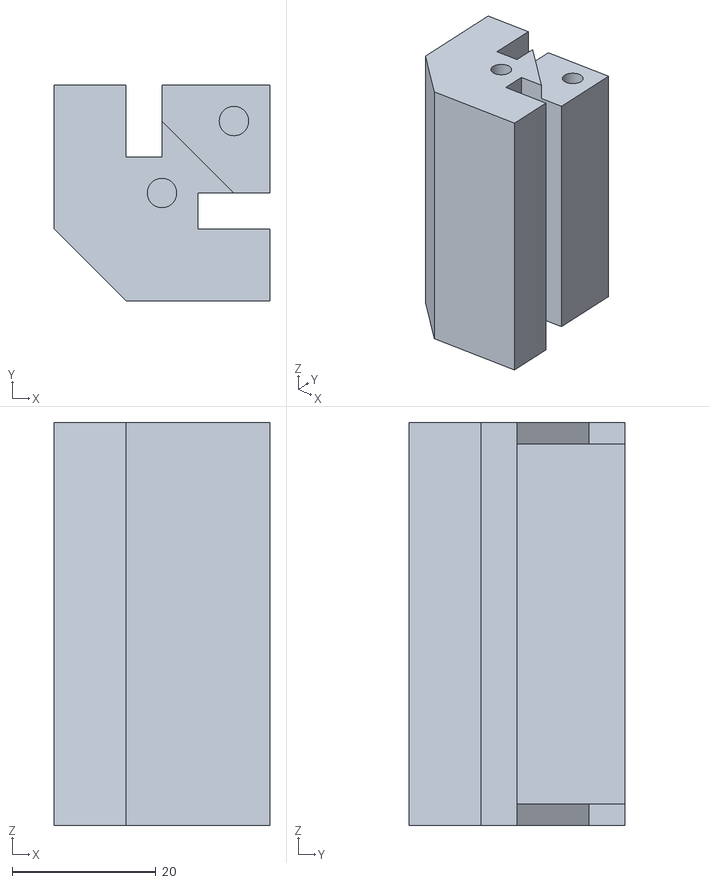
[picture p91: CAD file, 2025-08-16]
Ork/Production Files/corner.stl
30.0 x 30.0 x 56.0
