superbad64/OpenFighter/Personal Builds/Final Boss Neo/STL/top_left.stl

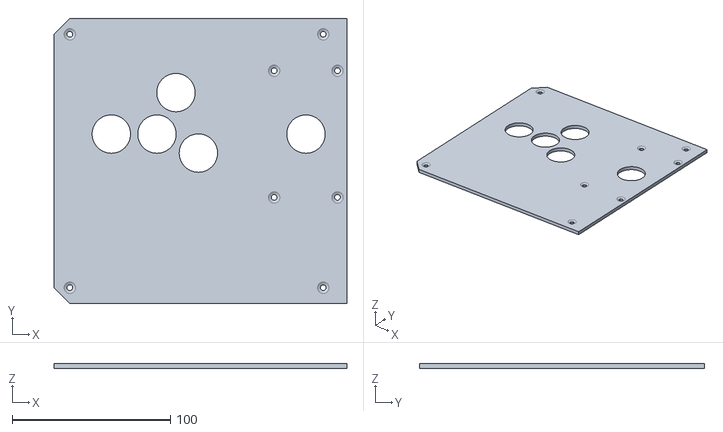
[picture p92: CAD file, 2025-08-16]
Personal Builds/Final Boss Neo/STL/top_left.stl
185.0 x 180.0 x 3.00
