superbad64/OpenFighter/Personal Builds/Miniboss Neo/Print files/stripes.stl

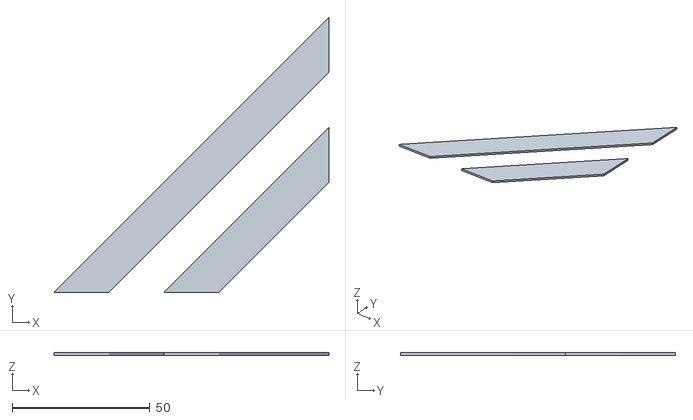
[picture p93: CAD file, 2025-08-16]
Personal Builds/Miniboss Neo/Print files/stripes.stl
100.0 x 100.0 x 1.00
