superbad64/OpenFighter/Personal Builds/Raijin/Production Files/topright.stl

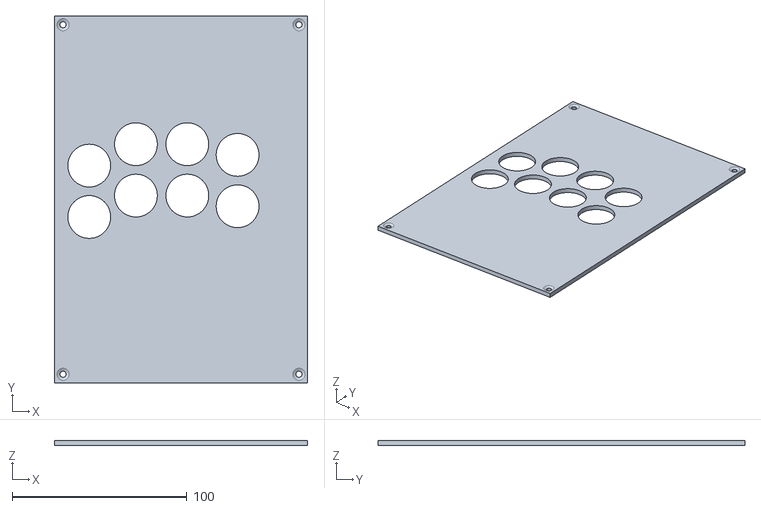
[picture p94: CAD file, 2025-08-24]
Personal Builds/Raijin/Production Files/topright.stl
145.0 x 210.0 x 3.00
