superbad64/OpenFighter/Unhinged/STL/right.stl

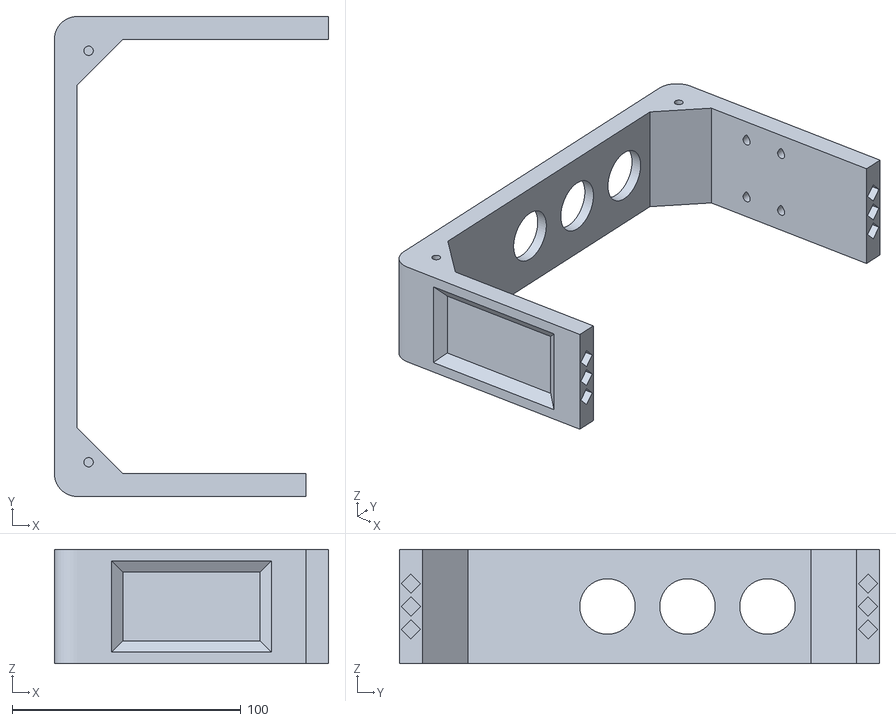
[picture p95: CAD file, 2025-02-27]
Unhinged/STL/right.stl
120.0 x 210.0 x 50.0
