superbad64/OpenFighter/Wanderer/Production Files/STL/post.stl

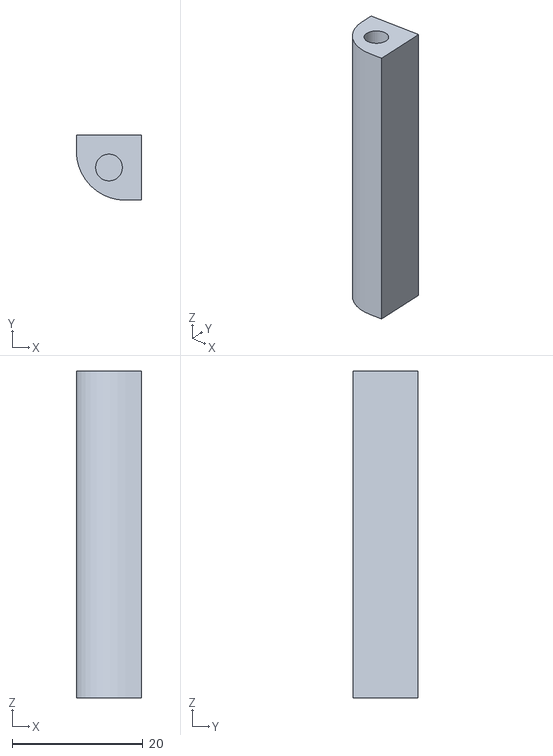
[picture p96: CAD file, 2025-03-14]
Wanderer/Production Files/STL/post.stl
10.0 x 10.0 x 50.0
