superbad64/OpenFighter/Personal Builds/Raijin/Production Files/sidesupport.stl

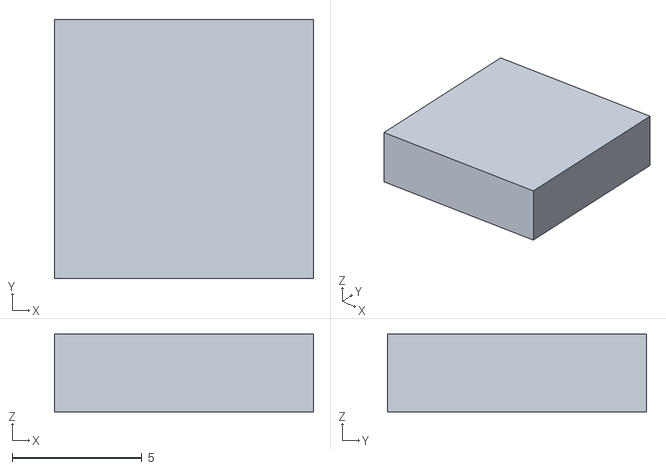
[picture p98: CAD file, 2025-08-24]
Personal Builds/Raijin/Production Files/sidesupport.stl
10.0 x 10.0 x 3.00
