superbad64/OpenFighter/Personal Builds/Raijin/Production Files/right.stl

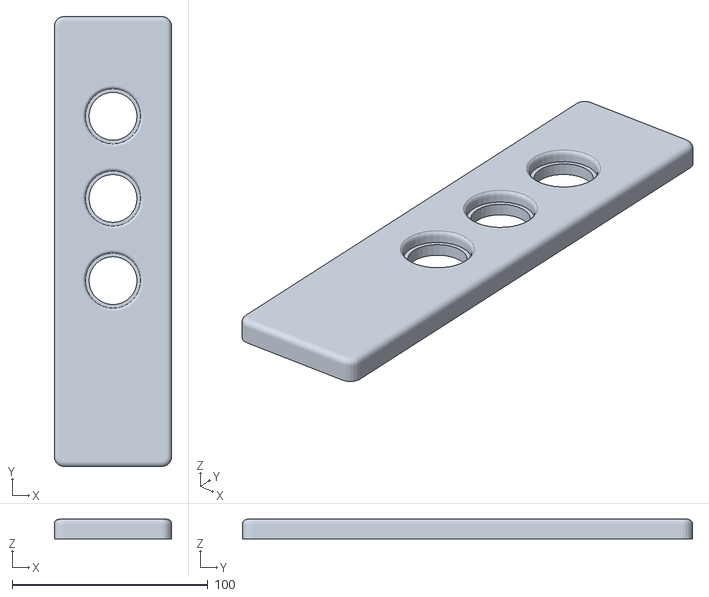
[picture p99: CAD file, 2025-08-24]
Personal Builds/Raijin/Production Files/right.stl
60.0 x 230.0 x 10.0
