superbad64/OpenFighter/Personal Builds/Raijin/Production Files/topleft.stl

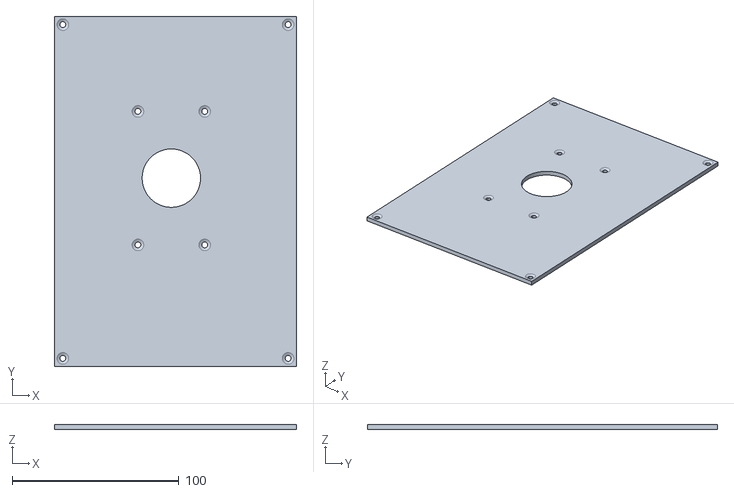
[picture p101: CAD file, 2025-08-24]
Personal Builds/Raijin/Production Files/topleft.stl
145.0 x 210.0 x 3.00
