superbad64/OpenFighter/Personal Builds/Raijin/Production Files/northeast.stl

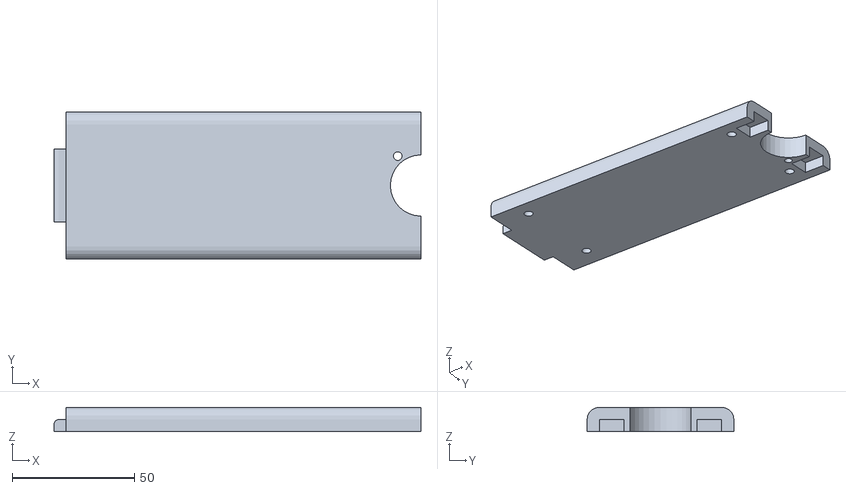
[picture p102: CAD file, 2025-08-24]
Personal Builds/Raijin/Production Files/northeast.stl
150.0 x 60.0 x 10.0
